QuadrarTecnologia/LoRaOne/LoRaONE Code Examples/2020.11.11- Webinar Embarcados - LoRaONE DevBoard Demo/Core/Src/usart.c

/**
  ******************************************************************************
  * File Name          : USART.c
  * Description        : This file provides code for the configuration
  *                      of the USART instances.
  ******************************************************************************
  * @attention
  *
  * <h2><center>&copy; Copyright (c) 2020 STMicroelectronics.
  * All rights reserved.</center></h2>
  *
  * This software component is licensed by ST under BSD 3-Clause license,
  * the "License"; You may not use this file except in compliance with the
  * License. You may obtain a copy of the License at:
  *                        opensource.org/licenses/BSD-3-Clause
  *
  ******************************************************************************
  */

/* Includes ------------------------------------------------------------------*/
#include "usart.h"

/* USER CODE BEGIN 0 */
#include "stdlib.h"
#include "stdio.h"
#include "string.h"

quadrar_uart_rx_t gps;
quadrar_uart_rx_t lora;


/* USER CODE END 0 */

UART_HandleTypeDef huart4;
UART_HandleTypeDef huart1;
UART_HandleTypeDef huart2;

/* UART4 init function */
void MX_UART4_Init(void)
{
  static uint8_t rx_byte;

  huart4.Instance = UART4;
  huart4.Init.BaudRate = 9600;
  huart4.Init.WordLength = UART_WORDLENGTH_8B;
  huart4.Init.StopBits = UART_STOPBITS_1;
  huart4.Init.Parity = UART_PARITY_NONE;
  huart4.Init.Mode = UART_MODE_TX_RX;
  huart4.Init.HwFlowCtl = UART_HWCONTROL_NONE;
  huart4.Init.OverSampling = UART_OVERSAMPLING_16;

  __HAL_RCC_UART4_CLK_ENABLE();

  if (HAL_UART_Init(&huart4) != HAL_OK)
  {
    Error_Handler();
  }

  HAL_UART_Receive_IT(&huart4, &rx_byte, sizeof(uint8_t));
}
/* USART1 init function */

void MX_USART1_UART_Init(void)
{
  static uint8_t rx_byte;

  huart1.Instance = USART1;
  huart1.Init.BaudRate = 9600;
  huart1.Init.WordLength = UART_WORDLENGTH_8B;
  huart1.Init.StopBits = UART_STOPBITS_1;
  huart1.Init.Parity = UART_PARITY_NONE;
  huart1.Init.Mode = UART_MODE_TX_RX;
  huart1.Init.HwFlowCtl = UART_HWCONTROL_NONE;
  huart1.Init.OverSampling = UART_OVERSAMPLING_16;

  __HAL_RCC_USART1_CLK_ENABLE();

  if (HAL_UART_Init(&huart1) != HAL_OK)
  {
    Error_Handler();
  }

  HAL_UART_Receive_IT(&huart1, &rx_byte, sizeof(uint8_t));
}
/* USART2 init function */

void MX_USART2_UART_Init(void)
{

  huart2.Instance = USART2;
  huart2.Init.BaudRate = 115200;
  huart2.Init.WordLength = UART_WORDLENGTH_8B;
  huart2.Init.StopBits = UART_STOPBITS_1;
  huart2.Init.Parity = UART_PARITY_NONE;
  huart2.Init.Mode = UART_MODE_TX_RX;
  huart2.Init.HwFlowCtl = UART_HWCONTROL_NONE;
  huart2.Init.OverSampling = UART_OVERSAMPLING_16;
  if (HAL_UART_Init(&huart2) != HAL_OK)
  {
    Error_Handler();
  }

}

void HAL_UART_MspInit(UART_HandleTypeDef* uartHandle)
{

  GPIO_InitTypeDef GPIO_InitStruct = {0};
  if(uartHandle->Instance==UART4)
  {
    /* UART4 clock enable */
    __HAL_RCC_UART4_CLK_ENABLE();

    __HAL_RCC_GPIOC_CLK_ENABLE();
    /**UART4 GPIO Configuration
    PC10     ------> UART4_TX
    PC11     ------> UART4_RX
    */
    GPIO_InitStruct.Pin = GPS_TX_Pin|GPS_RX_Pin;
    GPIO_InitStruct.Mode = GPIO_MODE_AF_PP;
    GPIO_InitStruct.Pull = GPIO_PULLUP;
    GPIO_InitStruct.Speed = GPIO_SPEED_FREQ_VERY_HIGH;
    GPIO_InitStruct.Alternate = GPIO_AF8_UART4;
    HAL_GPIO_Init(GPIOC, &GPIO_InitStruct);

    /* UART4 interrupt Init */
    HAL_NVIC_SetPriority(UART4_IRQn, 0, 0);
    HAL_NVIC_EnableIRQ(UART4_IRQn);
  /* USER CODE BEGIN UART4_MspInit 1 */

    // Enable the interrupt
    __HAL_UART_ENABLE_IT(uartHandle, UART_IT_RXNE);

  /* USER CODE END UART4_MspInit 1 */
  }
  else if(uartHandle->Instance==USART1)
  {
    /* USART1 clock enable */
    __HAL_RCC_USART1_CLK_ENABLE();

    __HAL_RCC_GPIOA_CLK_ENABLE();
    /**USART1 GPIO Configuration
    PA9     ------> USART1_TX
    PA10     ------> USART1_RX
    */
    GPIO_InitStruct.Pin = LoRa_TX_Pin|LoRa_RX_Pin;
    GPIO_InitStruct.Mode = GPIO_MODE_AF_PP;
    GPIO_InitStruct.Pull = GPIO_NOPULL;
    GPIO_InitStruct.Speed = GPIO_SPEED_FREQ_VERY_HIGH;
    GPIO_InitStruct.Alternate = GPIO_AF7_USART1;
    HAL_GPIO_Init(GPIOA, &GPIO_InitStruct);

    /* USART1 interrupt Init */
    HAL_NVIC_SetPriority(USART1_IRQn, 0, 0);
    HAL_NVIC_EnableIRQ(USART1_IRQn);
  /* USER CODE BEGIN USART1_MspInit 1 */

    // Enable the interrupt
    __HAL_UART_ENABLE_IT(uartHandle, UART_IT_RXNE);

  /* USER CODE END USART1_MspInit 1 */
  }
  else if(uartHandle->Instance==USART2)
  {
    /* USART2 clock enable */
    __HAL_RCC_USART2_CLK_ENABLE();

    __HAL_RCC_GPIOA_CLK_ENABLE();
    /**USART2 GPIO Configuration
    PA2     ------> USART2_TX
    PA3     ------> USART2_RX
    */
    GPIO_InitStruct.Pin = USART_TX_Pin|USART_RX_Pin;
    GPIO_InitStruct.Mode = GPIO_MODE_AF_PP;
    GPIO_InitStruct.Pull = GPIO_NOPULL;
    GPIO_InitStruct.Speed = GPIO_SPEED_FREQ_VERY_HIGH;
    GPIO_InitStruct.Alternate = GPIO_AF7_USART2;
    HAL_GPIO_Init(GPIOA, &GPIO_InitStruct);

  /* USER CODE BEGIN USART2_MspInit 1 */

    __HAL_UART_ENABLE_IT(uartHandle, UART_IT_RXNE);

  /* USER CODE END USART2_MspInit 1 */
  }
}

void HAL_UART_MspDeInit(UART_HandleTypeDef* uartHandle)
{

  if(uartHandle->Instance==UART4)
  {
    /* Peripheral clock disable */
    __HAL_RCC_UART4_CLK_DISABLE();

    /**UART4 GPIO Configuration
    PC10     ------> UART4_TX
    PC11     ------> UART4_RX
    */
    HAL_GPIO_DeInit(GPIOC, GPS_TX_Pin|GPS_RX_Pin);

    /* UART4 interrupt Deinit */
    HAL_NVIC_DisableIRQ(UART4_IRQn);
  }
  else if(uartHandle->Instance==USART1)
  {
    /* Peripheral clock disable */
    __HAL_RCC_USART1_CLK_DISABLE();

    /**USART1 GPIO Configuration
    PA9     ------> USART1_TX
    PA10     ------> USART1_RX
    */
    HAL_GPIO_DeInit(GPIOA, LoRa_TX_Pin|LoRa_RX_Pin);

    /* USART1 interrupt Deinit */
    HAL_NVIC_DisableIRQ(USART1_IRQn);
  }
  else if(uartHandle->Instance==USART2)
  {
    /* Peripheral clock disable */
    __HAL_RCC_USART2_CLK_DISABLE();

    /**USART2 GPIO Configuration
    PA2     ------> USART2_TX
    PA3     ------> USART2_RX
    */
    HAL_GPIO_DeInit(GPIOA, USART_TX_Pin|USART_RX_Pin);

  }
}

/* USER CODE BEGIN 1 */

int8_t uart_send_data(uint8_t* buf, uint8_t size)
{
	HAL_UART_Transmit(&huart1, buf, size,1000);
	return 0;
}

/**
* @brief   : Callback for the Uart reception interrupt
* @param   : uart pointer structure
* @retval  : none
*/
void HAL_UART_RxCpltCallback(UART_HandleTypeDef *huart)
{
	static uint8_t byte = 0;

	if(huart == NULL)
	{
		HAL_UART_Receive_IT(huart, &byte, 1);
	}
	else if (huart->Instance==USART1)
	{
		if(byte)
		{
			if (lora.pos >= sizeof(lora.bufferRx))
			{
				lora.pos = 0;
			}
			if(byte != 0x0d && byte != 0x0a)
			{
				lora.bufferRx[lora.pos++] = byte;
			}
			else if(lora.pos > 1)
			{
				lora.bufferRx[lora.pos++] = 0;
				memset((char*)lora.bufferData, 0x00, sizeof(lora.bufferData));
				strcpy((char*)lora.bufferData,(char*)lora.bufferRx);
				lora.pos = 0;
				lora.dataComplete = 1;
			}
		}
		HAL_UART_Receive_IT(huart, &byte, 1);
	}
	else if (huart->Instance==UART4)
	{
		if(byte)
		{
			if (gps.pos >= sizeof(gps.bufferRx))
			{
				gps.pos = 0;
			}
			if(byte != 0x0d && byte != 0x0a)
			{
				gps.bufferRx[gps.pos++] = byte;
			}
			else if(gps.pos > 1)
			{
				gps.bufferRx[gps.pos++] = 0;
				gps.pos = 0;
				if(strncmp(gps.bufferRx, "$GPRMC", strlen ("$GPRMC")) == 0)
				{
					memset((char*)gps.bufferData, 0x00, sizeof(gps.bufferData));
					strcpy((char*)gps.bufferData,(char*)gps.bufferRx);
					gps.dataComplete = 1;
				}
			}
		}
		HAL_UART_Receive_IT(huart, &byte, 1);
	}
}

/* USER CODE END 1 */

/************************ (C) COPYRIGHT STMicroelectronics *****END OF FILE****/
