QuadrarTecnologia/LoRaOne/LoRaONE Code Examples/2020.11.11- Webinar Embarcados - LoRaONE DevBoard Demo/Core/Src/rtc.c

/**
  ******************************************************************************
  * File Name          : RTC.c
  * Description        : This file provides code for the configuration
  *                      of the RTC instances.
  ******************************************************************************
  * @attention
  *
  * <h2><center>&copy; Copyright (c) 2020 STMicroelectronics.
  * All rights reserved.</center></h2>
  *
  * This software component is licensed by ST under BSD 3-Clause license,
  * the "License"; You may not use this file except in compliance with the
  * License. You may obtain a copy of the License at:
  *                        opensource.org/licenses/BSD-3-Clause
  *
  ******************************************************************************
  */

/* Includes ------------------------------------------------------------------*/
#include "rtc.h"

RTC_HandleTypeDef hrtc;

/* RTC init function */
void MX_RTC_Init(void)
{
  RTC_TimeTypeDef sTime = {0};
  RTC_DateTypeDef sDate = {0};

  /** Initialize RTC Only
  */
  hrtc.Instance = RTC;
  hrtc.Init.HourFormat = RTC_HOURFORMAT_24;
  hrtc.Init.AsynchPrediv = 127;
  hrtc.Init.SynchPrediv = 255;
  hrtc.Init.OutPut = RTC_OUTPUT_DISABLE;
  hrtc.Init.OutPutPolarity = RTC_OUTPUT_POLARITY_HIGH;
  hrtc.Init.OutPutType = RTC_OUTPUT_TYPE_OPENDRAIN;
  if (HAL_RTC_Init(&hrtc) != HAL_OK)
  {
    Error_Handler();
  }

  /** Initialize RTC and set the Time and Date
  */
  sTime.Hours = 0x0;
  sTime.Minutes = 0x0;
  sTime.Seconds = 0x0;
  sTime.DayLightSaving = RTC_DAYLIGHTSAVING_NONE;
  sTime.StoreOperation = RTC_STOREOPERATION_RESET;
  if (HAL_RTC_SetTime(&hrtc, &sTime, RTC_FORMAT_BCD) != HAL_OK)
  {
    Error_Handler();
  }
  sDate.WeekDay = RTC_WEEKDAY_MONDAY;
  sDate.Month = RTC_MONTH_JANUARY;
  sDate.Date = 0x1;
  sDate.Year = 0x0;

  if (HAL_RTC_SetDate(&hrtc, &sDate, RTC_FORMAT_BCD) != HAL_OK)
  {
    Error_Handler();
  }
  /** Enable the WakeUp
  */
  if (HAL_RTCEx_SetWakeUpTimer_IT(&hrtc, 0, RTC_WAKEUPCLOCK_CK_SPRE_17BITS) != HAL_OK)
  {
    Error_Handler();
  }

}

void HAL_RTC_MspInit(RTC_HandleTypeDef* rtcHandle)
{

  if(rtcHandle->Instance==RTC)
  {
    /* RTC clock enable */
    __HAL_RCC_RTC_ENABLE();

    /* RTC interrupt Init */
    HAL_NVIC_SetPriority(RTC_WKUP_IRQn, 0, 0);
    HAL_NVIC_EnableIRQ(RTC_WKUP_IRQn);
  }
}

void HAL_RTC_MspDeInit(RTC_HandleTypeDef* rtcHandle)
{

  if(rtcHandle->Instance==RTC)
  {
    /* Peripheral clock disable */
    __HAL_RCC_RTC_DISABLE();

    /* RTC interrupt Deinit */
    HAL_NVIC_DisableIRQ(RTC_WKUP_IRQn);
  }
}

/* USER CODE BEGIN 1 */
/**
* @brief   : Sets RTC alarm to wake up from stop mode
* @param   : wakeUpTime Seconds to wake up
* @retval  : Status code
*/
int8_t quadrar_rtc_set_wakeup(uint32_t secondsWakeUpTime)
{
	//Disables the RTC Wakeup timer
    HAL_RTCEx_DeactivateWakeUpTimer(&hrtc);

    if(secondsWakeUpTime)
    {
      //Sets the RTC Wake Up with 1Hz Ckock
      HAL_RTCEx_SetWakeUpTimer_IT(&hrtc, secondsWakeUpTime, RTC_WAKEUPCLOCK_CK_SPRE_16BITS);
    }
    return 0;
}
/* USER CODE END 1 */

/************************ (C) COPYRIGHT STMicroelectronics *****END OF FILE****/
