QuadrarTecnologia/LoRaOne/LoRaONE Code Examples/2020.11.11- Webinar Embarcados - LoRaONE DevBoard Demo/Core/quadrar/dwt_stm32_delay.h

#ifndef DWT_STM32_DELAY_H_
#define DWT_STM32_DELAY_H_

#include "stm32l1xx_hal.h"
/**
 * @brief Initializes DWT_Cycle_Count for DWT_Delay_us function
 * @return Error DWT counter
 * 1: DWT counter Error
 * 0: DWT counter works
 */
uint32_t DWT_Delay_Init(void);

/**
 * @brief This function provides a delay (in microseconds)
 * @param microseconds: delay in microseconds
 */
__STATIC_INLINE void dwt_delay_us(volatile uint32_t microseconds)
{
	uint32_t clk_cycle_start = DWT->CYCCNT;
	/* Go to number of cycles for system */
	microseconds *= (HAL_RCC_GetHCLKFreq() / 1000000);
	/* Delay till end */
	while ((DWT->CYCCNT - clk_cycle_start) < microseconds);
}

__STATIC_INLINE void dwt_delay_ns(volatile uint64_t nanoseconds)
{
	uint32_t clk_cycle_start = DWT->CYCCNT;
	/* Go to number of cycles for system */
	nanoseconds = (nanoseconds * HAL_RCC_GetHCLKFreq());
	nanoseconds /= 1000000000;
	/* Delay till end */
	while ((DWT->CYCCNT - clk_cycle_start) < nanoseconds);
}

#endif /* DWT_STM32_DELAY_H_ */
